Giraffasax/SpUnLy58/Reference/SpUnLy58_v1_PCB_bottom.png

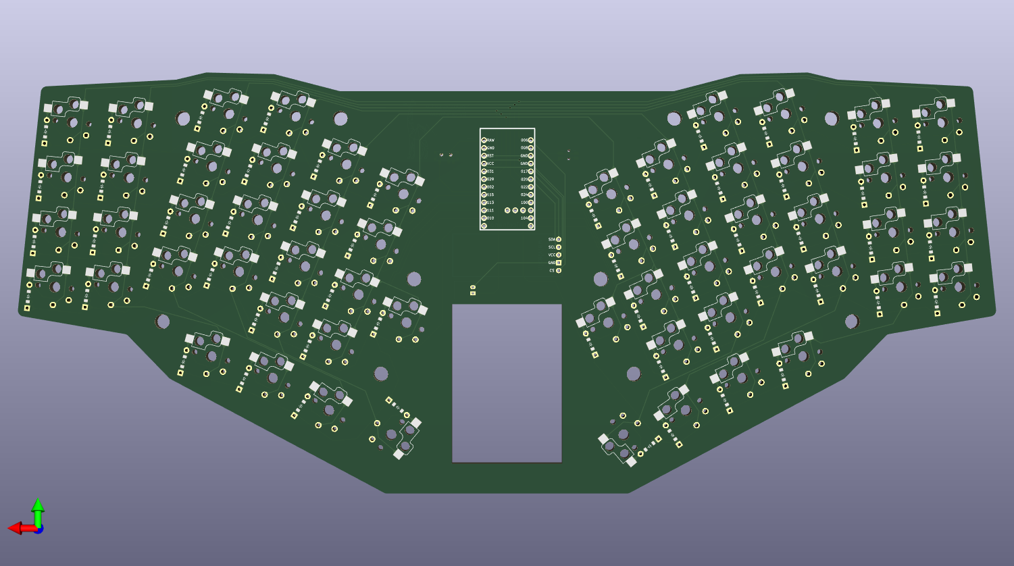
Reference/SpUnLy58_v1_PCB_bottom.png
